OrturanoLabs/isomorphic_keyboard/firmware/experiments/scan_low_rate_i2c/up5k.pcf

set_io --warn-no-port reset_n 10
set_io --warn-no-port clk_in 35

set_io --warn-no-port clk_out 31
set_io --warn-no-port data 34
set_io --warn-no-port latch 38

set_io --warn-no-port package_sda 20
set_io --warn-no-port package_scl 21

set_io --warn-no-port led_blue 40
set_io --warn-no-port led_green 39
set_io --warn-no-port led_red 41

set_io --warn-no-port trigger 27
